sfraint/wireless-n64-controller/images/controller_internals.jpg

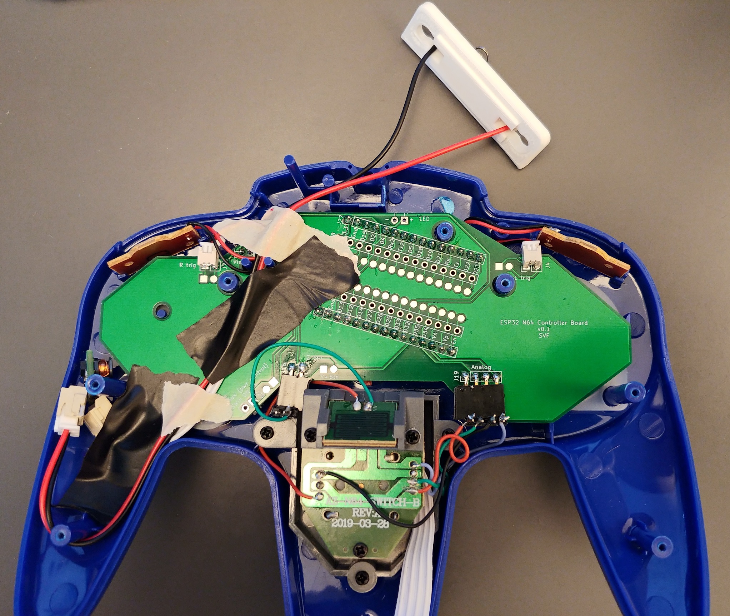
images/controller_internals.jpg
